eljotx/SDR-TRX-on-ESP32-A1S/software/ver1_1/arduino/fir_coeffs_81Taps_44100_200_20000.h

float coeffs_hilbert_81Taps_44100_200_20000[] = {
 0.000000000000000000,
 0.000042434740807478,
 0.000000000000000000,
 0.000194147043699295,
 0.000000000000000000,
 0.000496066366371690,
 0.000000000000000000,
 0.000994950573157256,
 0.000000000000000000,
 0.001743612123463702,
 0.000000000000000000,
 0.002801476094220583,
 0.000000000000000000,
 0.004235758940422858,
 0.000000000000000000,
 0.006123722541518531,
 0.000000000000000000,
 0.008556744921891134,
 0.000000000000000000,
 0.011647474341045674,
 0.000000000000000000,
 0.015542350896695834,
 0.000000000000000000,
 0.020443871826957602,
 0.000000000000000000,
 0.026651580363050011,
 0.000000000000000000,
 0.034641742208750964,
 0.000000000000000000,
 0.045234644942154088,
 0.000000000000000000,
 0.059985390641862417,
 0.000000000000000000,
 0.082244567263393492,
 0.000000000000000000,
 0.120763605480144046,
 0.000000000000000000,
 0.207718663854237096,
 0.000000000000000000,
 0.633008825839523892,
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
 
};
float coeffs_delay_81[] = {
 0.000000000000000000,
 0.000000000000000000,
 0.000000000000000000,
 0.000000000000000000,
 0.000000000000000000,
 0.000000000000000000,
 0.000000000000000000,
 0.000000000000000000,
 0.000000000000000000,
 0.000000000000000000,
 0.000000000000000000,
 0.000000000000000000,
 0.000000000000000000,
 0.000000000000000000,
 0.000000000000000000,
 0.000000000000000000,
 0.000000000000000000,
 0.000000000000000000,
 0.000000000000000000,
 0.000000000000000000,
 0.000000000000000000,
 0.000000000000000000,
 0.000000000000000000,
 0.000000000000000000,
 0.000000000000000000,
 0.000000000000000000,
 0.000000000000000000,
 0.000000000000000000,
 0.000000000000000000,
 0.000000000000000000,
 0.000000000000000000,
 0.000000000000000000,
 0.000000000000000000,
 0.000000000000000000,
 0.000000000000000000,
 0.000000000000000000,
 0.000000000000000000,
 0.000000000000000000,
 0.000000000000000000,
 0.000000000000000000,
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
   
};
