eljotx/SDR-TRX-on-ESP32-A1S/software/ver1_1/arduino/hb_24_81.h

float hilbert_24_81[] = {
 0.000000000000000000,
 0.001010454500352403,
 0.000000000000000000,
 0.001603255859532541,
 0.000000000000000000,
 0.002375777373301829,
 0.000000000000000000,
 0.003359687137242189,
 0.000000000000000000,
 0.004590635761249413,
 0.000000000000000000,
 0.006109489383812925,
 0.000000000000000000,
 0.007964297313100987,
 0.000000000000000000,
 0.010213412952175432,
 0.000000000000000000,
 0.012930468263199312,
 0.000000000000000000,
 0.016212424790148887,
 0.000000000000000000,
 0.020192942601517865,
 0.000000000000000000,
 0.025065406074645170,
 0.000000000000000000,
 0.031124561828039420,
 0.000000000000000000,
 0.038846735096519376,
 0.000000000000000000,
 0.049057623633961871,
 0.000000000000000000,
 0.063323771844953539,
 0.000000000000000000,
 0.085014919370140635,
 0.000000000000000000,
 0.122915449545254782,
 0.000000000000000000,
 0.209280397932459006,
 0.000000000000000000,
 0.634558987132335495,
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
 
};
float coeffs_delay_81[] = {
 0.000000000000000000,
 0.000000000000000000,
 0.000000000000000000,
 0.000000000000000000,
 0.000000000000000000,
 0.000000000000000000,
 0.000000000000000000,
 0.000000000000000000,
 0.000000000000000000,
 0.000000000000000000,
 0.000000000000000000,
 0.000000000000000000,
 0.000000000000000000,
 0.000000000000000000,
 0.000000000000000000,
 0.000000000000000000,
 0.000000000000000000,
 0.000000000000000000,
 0.000000000000000000,
 0.000000000000000000,
 0.000000000000000000,
 0.000000000000000000,
 0.000000000000000000,
 0.000000000000000000,
 0.000000000000000000,
 0.000000000000000000,
 0.000000000000000000,
 0.000000000000000000,
 0.000000000000000000,
 0.000000000000000000,
 0.000000000000000000,
 0.000000000000000000,
 0.000000000000000000,
 0.000000000000000000,
 0.000000000000000000,
 0.000000000000000000,
 0.000000000000000000,
 0.000000000000000000,
 0.000000000000000000,
 0.000000000000000000,
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
};
