eljotx/SDR-TRX-on-ESP32-A1S/software/ver1_1/arduino/fir_coeffs_47Taps_44100_200_20000.h

float coeffs_hilbert_47Taps_44100_200_20000[] = {
 0.001600195947024479,
 0.000000000000000000,
 0.003437992254135160,
 0.000000000000000000,
 0.006260681117767582,
 0.000000000000000000,
 0.010370974060687288,
 0.000000000000000000,
 0.016157802099483028,
 0.000000000000000000,
 0.024167385289310141,
 0.000000000000000000,
 0.035263294679112683,
 0.000000000000000000,
 0.051012358702287056,
 0.000000000000000000,
 0.074743966232958453,
 0.000000000000000000,
 0.115160180421751773,
 0.000000000000000000,
 0.204384725601037209,
 0.000000000000000000,
 0.632547080709674914,
 0.000000000000000000,
-0.632547080709674914,
 0.000000000000000000,
-0.204384725601037209,
 0.000000000000000000,
-0.115160180421751773,
 0.000000000000000000,
-0.074743966232958453,
 0.000000000000000000,
-0.051012358702287056,
 0.000000000000000000,
-0.035263294679112683,
 0.000000000000000000,
-0.024167385289310141,
 0.000000000000000000,
-0.016157802099483028,
 0.000000000000000000,
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
 
};
float coeffs_delay_47[] = {
 0.000000000000000000,
 0.000000000000000000,
 0.000000000000000000,
 0.000000000000000000,
 0.000000000000000000,
 0.000000000000000000,
 0.000000000000000000,
 0.000000000000000000,
 0.000000000000000000,
 0.000000000000000000,
 0.000000000000000000,
 0.000000000000000000,
 0.000000000000000000,
 0.000000000000000000,
 0.000000000000000000,
 0.000000000000000000,
 0.000000000000000000,
 0.000000000000000000,
 0.000000000000000000,
 0.000000000000000000,
 0.000000000000000000,
 0.000000000000000000,
 0.000000000000000000,
 1.000000000000000000,
 0.000000000000000000,
 0.000000000000000000,
 0.000000000000000000,
 0.000000000000000000,
 0.000000000000000000,
 0.000000000000000000,
 0.000000000000000000,
 0.000000000000000000,
 0.000000000000000000,
 0.000000000000000000,
 0.000000000000000000,
 0.000000000000000000,
 0.000000000000000000,
 0.000000000000000000,
 0.000000000000000000,
 0.000000000000000000,
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
   
};
